amstan/tr2/pictures/board/microscope-prefab-1.jpg

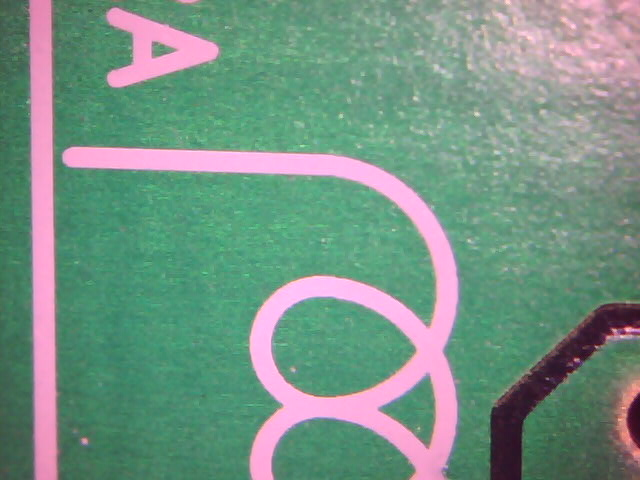
pictures/board/microscope-prefab-1.jpg
