amstan/tr2/pictures/board/microscope-prefab-2.jpg

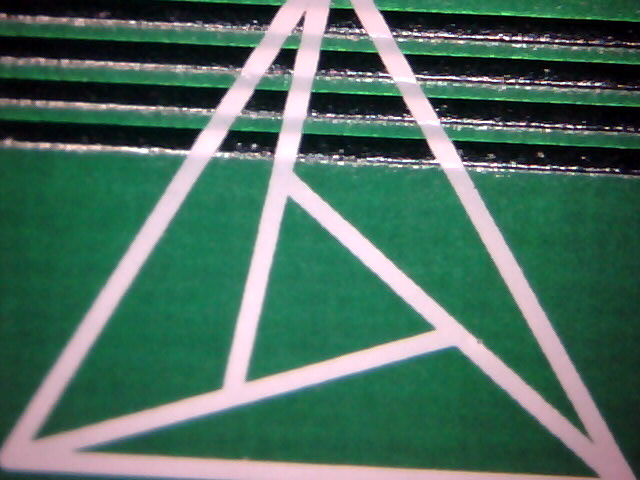
pictures/board/microscope-prefab-2.jpg
