amstan/tr2/pictures/board/microscope-prefab-3.jpg

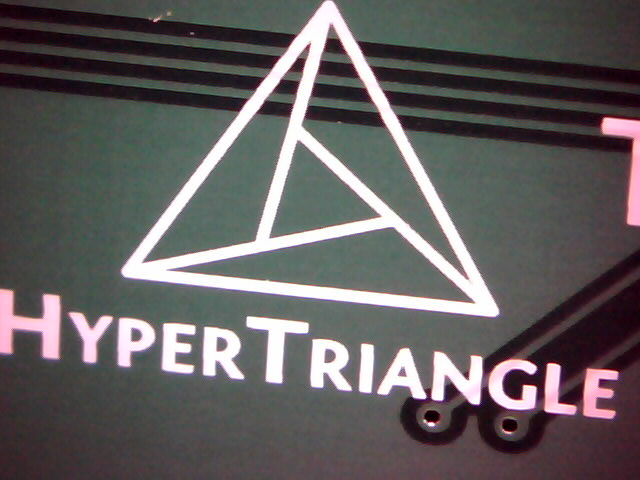
pictures/board/microscope-prefab-3.jpg
