amstan/tr2/pictures/board/microscope-prefab-4.jpg

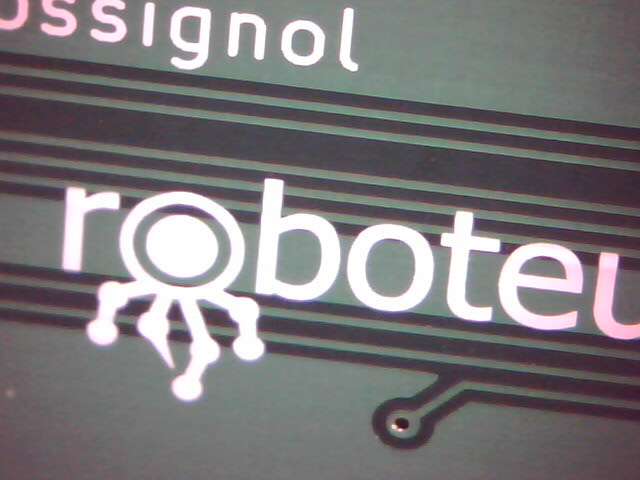
pictures/board/microscope-prefab-4.jpg
