amstan/tr2/pictures/board/microscope-prefab-6.jpg

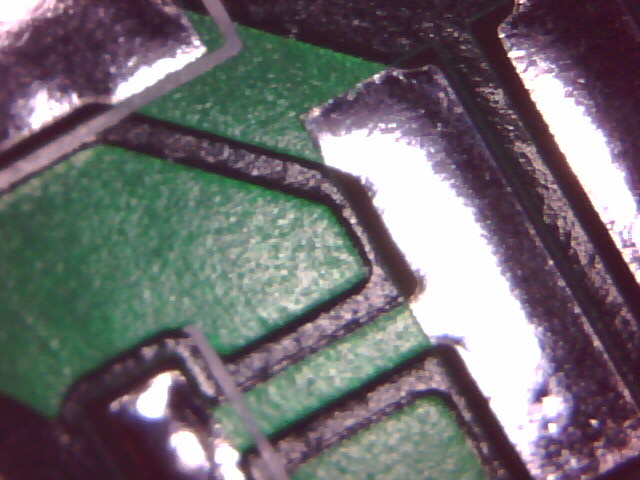
pictures/board/microscope-prefab-6.jpg
