amstan/tr2/pictures/board/microscope-prefab-7.jpg

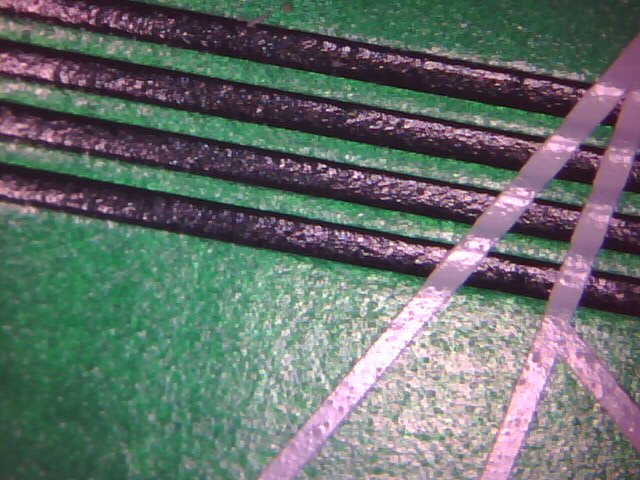
pictures/board/microscope-prefab-7.jpg
